benetherington/heartrate/heartrate.h

#ifndef Heartrate_h
#define Heartrate_h

const unsigned char heartNoInterior [] PROGMEM = {
	0x07, 0xc0, 0x01, 0xf0, 0x00, 0x08, 0x38, 0x0e, 0x08, 0x00, 0x10, 0x04, 0x10, 0x04, 0x00, 0x20, 
	0x02, 0x20, 0x02, 0x00, 0x20, 0x02, 0x20, 0x02, 0x00, 0x40, 0x01, 0x40, 0x01, 0x00, 0x40, 0x01, 
	0x40, 0x01, 0x00, 0x40, 0x00, 0x80, 0x01, 0x00, 0x80, 0x00, 0x00, 0x00, 0x80, 0x80, 0x00, 0x00, 
	0x00, 0x80, 0x80, 0x00, 0x00, 0x00, 0x80, 0x40, 0x00, 0x00, 0x01, 0x00, 0x40, 0x00, 0x00, 0x01, 
	0x00, 0x40, 0x00, 0x00, 0x01, 0x00, 0x40, 0x00, 0x00, 0x01, 0x00, 0x20, 0x00, 0x00, 0x02, 0x00, 
	0x20, 0x00, 0x00, 0x02, 0x00, 0x10, 0x00, 0x00, 0x04, 0x00, 0x10, 0x00, 0x00, 0x04, 0x00, 0x08, 
	0x00, 0x00, 0x08, 0x00, 0x04, 0x00, 0x00, 0x10, 0x00, 0x02, 0x00, 0x00, 0x20, 0x00, 0x01, 0x00, 
	0x00, 0x40, 0x00, 0x00, 0x80, 0x00, 0x80, 0x00, 0x00, 0x40, 0x01, 0x00, 0x00, 0x00, 0x20, 0x02, 
	0x00, 0x00, 0x00, 0x10, 0x04, 0x00, 0x00, 0x00, 0x08, 0x08, 0x00, 0x00, 0x00, 0x04, 0x10, 0x00, 
	0x00, 0x00, 0x02, 0x20, 0x00, 0x00, 0x00, 0x01, 0x40, 0x00, 0x00, 0x00, 0x00, 0x80, 0x00, 0x00
};
const unsigned char heartWithInterior [] PROGMEM = {
	0x07, 0xc0, 0x01, 0xf0, 0x00, 0x08, 0x38, 0x0e, 0x08, 0x00, 0x13, 0x84, 0x10, 0xe4, 0x00, 0x27, 
	0xf2, 0x27, 0xf2, 0x00, 0x2f, 0xfa, 0x2f, 0xfa, 0x00, 0x4f, 0xf9, 0x4f, 0xf9, 0x00, 0x5f, 0xfd, 
	0x5f, 0xfd, 0x00, 0x5f, 0xfc, 0x9f, 0xfd, 0x00, 0x9f, 0xfe, 0x3f, 0xfc, 0x80, 0xbf, 0xff, 0xff, 
	0xfe, 0x80, 0x9f, 0xff, 0xff, 0xfc, 0x80, 0x5f, 0xff, 0xff, 0xfd, 0x00, 0x5f, 0xff, 0xff, 0xfd, 
	0x00, 0x5f, 0xff, 0xff, 0xfd, 0x00, 0x4f, 0xff, 0xff, 0xf9, 0x00, 0x2f, 0xff, 0xff, 0xfa, 0x00, 
	0x27, 0xff, 0xff, 0xf2, 0x00, 0x17, 0xff, 0xff, 0xf4, 0x00, 0x13, 0xff, 0xff, 0xe4, 0x00, 0x09, 
	0xff, 0xff, 0xc8, 0x00, 0x04, 0xff, 0xff, 0x90, 0x00, 0x02, 0x7f, 0xff, 0x20, 0x00, 0x01, 0x3f, 
	0xfe, 0x40, 0x00, 0x00, 0x9f, 0xfc, 0x80, 0x00, 0x00, 0x4f, 0xf9, 0x00, 0x00, 0x00, 0x27, 0xf2, 
	0x00, 0x00, 0x00, 0x13, 0xe4, 0x00, 0x00, 0x00, 0x09, 0xc8, 0x00, 0x00, 0x00, 0x04, 0x90, 0x00, 
	0x00, 0x00, 0x02, 0x20, 0x00, 0x00, 0x00, 0x01, 0x40, 0x00, 0x00, 0x00, 0x00, 0x80, 0x00, 0x00
};
// 'heart_interior', 33x32px
const unsigned char heartInterior [] PROGMEM = {
	0x00, 0x00, 0x00, 0x00, 0x00, 0x00, 0x00, 0x00, 0x00, 0x00, 0x03, 0x80, 0x00, 0xe0, 0x00, 0x07, 
	0xf0, 0x07, 0xf0, 0x00, 0x0f, 0xf8, 0x0f, 0xf8, 0x00, 0x0f, 0xf8, 0x0f, 0xf8, 0x00, 0x1f, 0xfc, 
	0x1f, 0xfc, 0x00, 0x1f, 0xfc, 0x1f, 0xfc, 0x00, 0x1f, 0xfe, 0x3f, 0xfc, 0x00, 0x3f, 0xff, 0xff, 
	0xfe, 0x00, 0x1f, 0xff, 0xff, 0xfc, 0x00, 0x1f, 0xff, 0xff, 0xfc, 0x00, 0x1f, 0xff, 0xff, 0xfc, 
	0x00, 0x1f, 0xff, 0xff, 0xfc, 0x00, 0x0f, 0xff, 0xff, 0xf8, 0x00, 0x0f, 0xff, 0xff, 0xf8, 0x00, 
	0x07, 0xff, 0xff, 0xf0, 0x00, 0x07, 0xff, 0xff, 0xf0, 0x00, 0x03, 0xff, 0xff, 0xe0, 0x00, 0x01, 
	0xff, 0xff, 0xc0, 0x00, 0x00, 0xff, 0xff, 0x80, 0x00, 0x00, 0x7f, 0xff, 0x00, 0x00, 0x00, 0x3f, 
	0xfe, 0x00, 0x00, 0x00, 0x1f, 0xfc, 0x00, 0x00, 0x00, 0x0f, 0xf8, 0x00, 0x00, 0x00, 0x07, 0xf0, 
	0x00, 0x00, 0x00, 0x03, 0xe0, 0x00, 0x00, 0x00, 0x01, 0xc0, 0x00, 0x00, 0x00, 0x00, 0x80, 0x00, 
	0x00, 0x00, 0x00, 0x00, 0x00, 0x00, 0x00, 0x00, 0x00, 0x00, 0x00, 0x00, 0x00, 0x00, 0x00, 0x00
};



#endif
